Technical-1/EEL4599-Final-Project/Diagrams/schematic/BaseNode.kicad_sch

## KiCad design Diagrams/schematic/BaseNode.kicad_sch (2026-05-30)

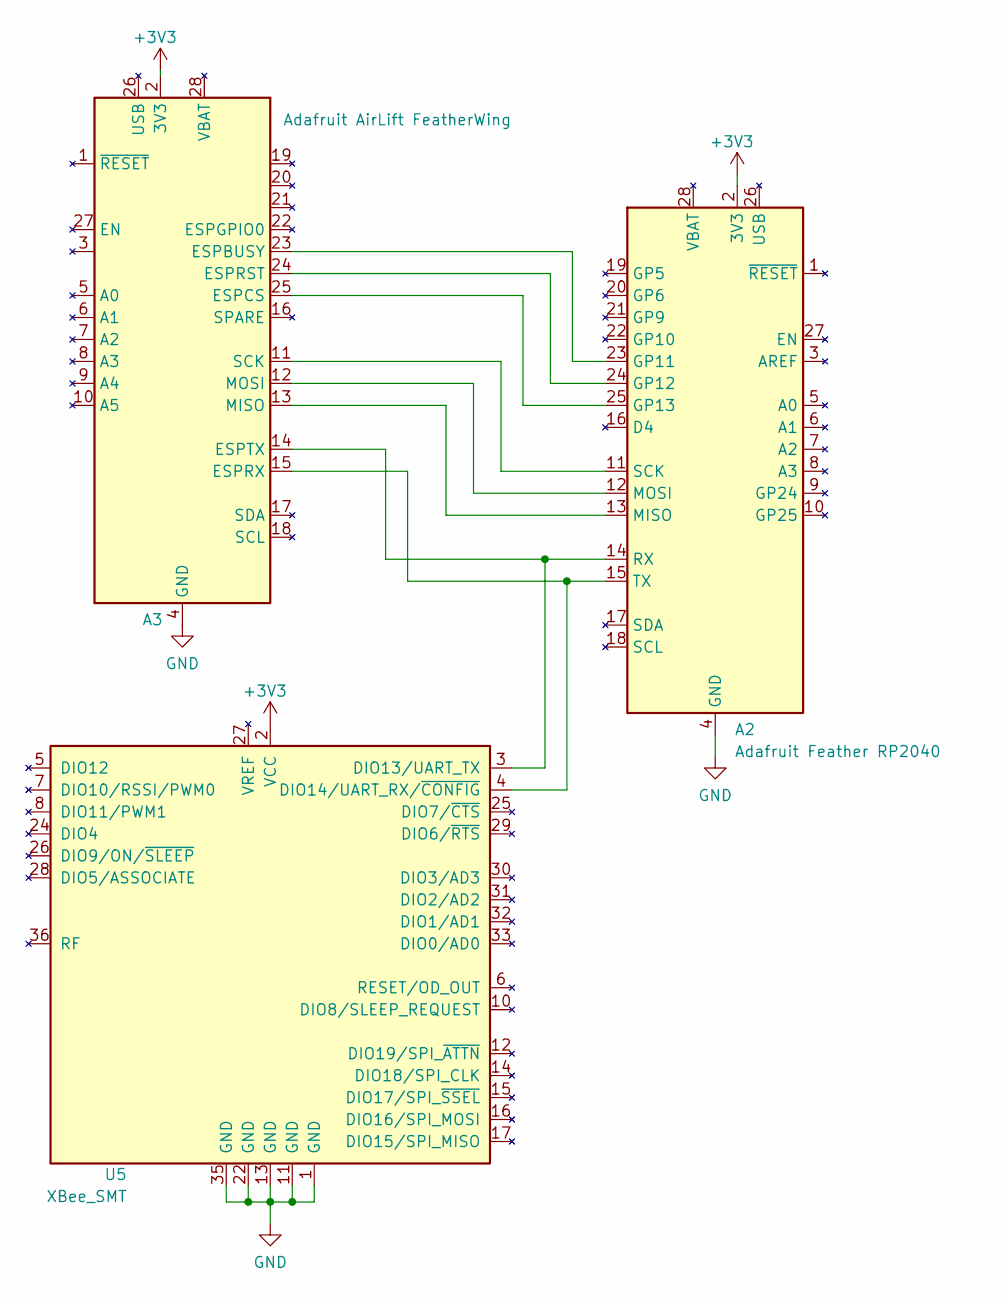
[picture p2: schematic BaseNode.kicad_sch]

Parts:
A2: Adafruit Feather RP2040; Adafruit_Feather
A3: Adafruit AirLift FeatherWing; Adafruit_Feather
U5: XBee_SMT; Digi_XBee_SMT

Connections:
+3V3: A2.2 (3V3), A3.2 (3V3), U5.2 (VCC)
GND: A2.4 (GND), A3.4 (GND), U5.1 (GND), U5.11 (GND), U5.13 (GND), U5.22 (GND), U5.35 (GND)
unnamed: A2.11 (SCK), A3.11 (SCK)
unnamed: A2.12 (MOSI), A3.12 (MOSI)
unnamed: A2.13 (MISO), A3.13 (MISO)
unnamed: A2.14 (RX), A3.14 (ESPTX), U5.3 (DIO13/UART_TX)
unnamed: A2.15 (TX), A3.15 (ESPRX), U5.4 (DIO14/UART_RX/~CONFIG)
unnamed: A2.23 (GP11), A3.23 (ESPBUSY)
unnamed: A2.24 (GP12), A3.24 (ESPRST)
unnamed: A2.25 (GP13), A3.25 (ESPCS)
