Technical-1/EEL4599-Final-Project/Diagrams/schematic/LightNode.kicad_sch

## KiCad design Diagrams/schematic/LightNode.kicad_sch (2026-05-30)

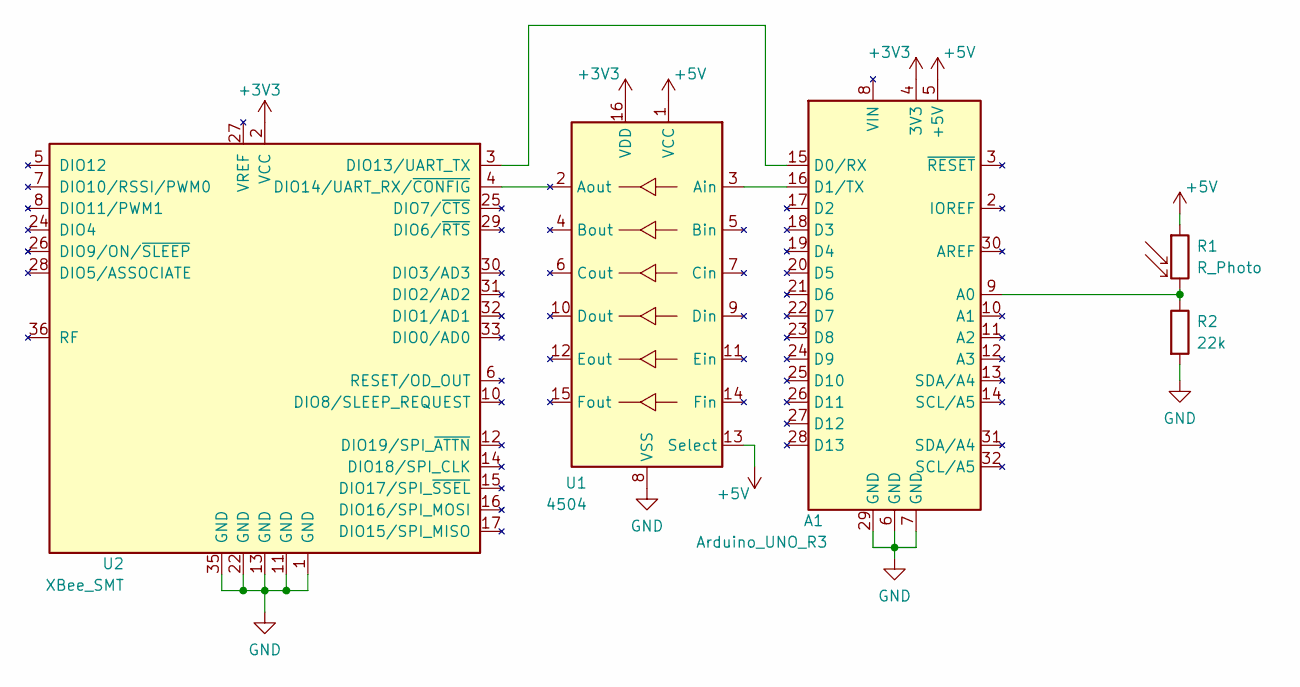
[picture p3: schematic LightNode.kicad_sch]

Parts:
A1: Arduino_UNO_R3
R1: R_Photo
R2: 22k
U1: 4504
U2: XBee_SMT; Digi_XBee_SMT

Connections:
+3V3: A1.4 (3V3), U1.16 (VDD), U2.2 (VCC)
+5V: A1.5 (+5V), R1.1, U1.1 (VCC), U1.13 (Select)
GND: A1.6 (GND), A1.7 (GND), A1.29 (GND), R2.2, U1.8 (VSS), U2.1 (GND), U2.11 (GND), U2.13 (GND), U2.22 (GND), U2.35 (GND)
unnamed: A1.9 (A0), R1.2, R2.1
unnamed: A1.15 (D0/RX), U2.3 (DIO13/UART_TX)
unnamed: A1.16 (D1/TX), U1.3 (Ain)
unnamed: U1.2 (Aout), U2.4 (DIO14/UART_RX/~CONFIG)
