Technical-1/EEL4599-Final-Project/Diagrams/schematic/TempNode.kicad_sch

## KiCad design Diagrams/schematic/TempNode.kicad_sch (2026-05-30)

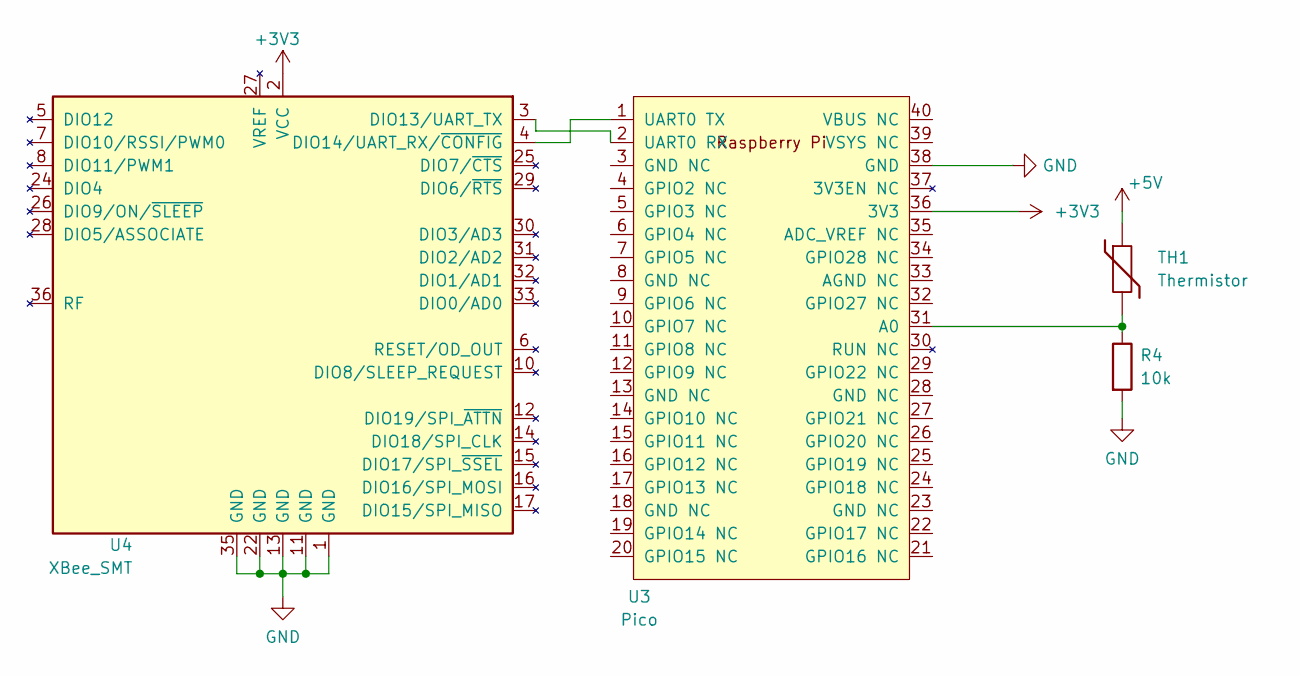
[picture p4: schematic TempNode.kicad_sch]

Parts:
R4: 10k
TH1: Thermistor
U3: Pico; RPi_Pico_SMD_TH
U4: XBee_SMT; Digi_XBee_SMT

Connections:
+3V3: U3.36 (3V3), U4.2 (VCC)
+5V: TH1.1
GND: R4.2, U3.38 (GND), U4.1 (GND), U4.11 (GND), U4.13 (GND), U4.22 (GND), U4.35 (GND)
unnamed: R4.1, TH1.2, U3.31 (GPIO26)
unnamed: U3.1 (GPIO0), U4.4 (DIO14/UART_RX/~CONFIG)
unnamed: U3.2 (GPIO1), U4.3 (DIO13/UART_TX)
